Kasn-w/omnitrix-replica/omitrix/activate.h

const unsigned char activate[] = {
0x52, 0x49, 0x46, 0x46, 0xBE, 0xAD, 0x00, 0x00, 0x57, 0x41, 0x56, 0x45, 0x66, 0x6D, 0x74, 0x20, 
0x10, 0x00, 0x00, 0x00, 0x01, 0x00, 0x02, 0x00, 0x80, 0x3E, 0x00, 0x00, 0x00, 0xFA, 0x00, 0x00, 
0x04, 0x00, 0x10, 0x00, 0x64, 0x61, 0x74, 0x61, 0xE4, 0xAC, 0x00, 0x00, 0x00, 0x00, 0xFD, 0xFF, 
0x00, 0x00, 0x03, 0x00, 0x00, 0x00, 0xE5, 0xF9, 0x00, 0x00, 0x03, 0x00, 0xE9, 0xF9, 0xE6, 0xF9, 
0xFE, 0xFF, 0xFF, 0xFF, 0x03, 0x00, 0xE6, 0xF9, 0xE2, 0xF9, 0x05, 0x00, 0x06, 0x00, 0xE0, 0xF9, 
0xE3, 0xF9, 0x09, 0x00, 0x07, 0x00, 0xFA, 0xFF, 0xF4, 0xFF, 0xEC, 0xF9, 0xF4, 0xF9, 0xFB, 0xFF, 
0xF7, 0xFF, 0x08, 0x00, 0xEF, 0xF9, 0xDE, 0xF9, 0xFB, 0xFF, 0x07, 0x00, 0xE8, 0xF9, 0xE8, 0xF9, 
0x00, 0x00, 0xFA, 0xFF, 0x06, 0x00, 0xEE, 0xF9, 0xF7, 0xFF, 0xFD, 0xFF, 0x0C, 0x00, 0x00, 0x00, 
0xF5, 0xFF, 0xEC, 0xF9, 0x04, 0x00, 0xFC, 0xFF, 0xEA, 0xF9, 0xE6, 0xF9, 0xFB, 0xFF, 0x06, 0x00, 
0xF1, 0xF9, 0xE1, 0xF9, 0xFB, 0xFF, 0x09, 0x00, 0xE7, 0xF9, 0xDE, 0xF9, 0xE6, 0xF9, 0x0A, 0x00, 
0x05, 0x00, 0xDF, 0xF9, 0xE1, 0xF9, 0x06, 0x00, 0xF2, 0xF9, 0xFE, 0xFF, 0xF6, 0xFF, 0xE3, 0xF9, 
0xED, 0xF9, 0x0C, 0x00, 0x01, 0x00, 0xDC, 0xF9, 0xE5, 0xF9, 0x06, 0x00, 0xFF, 0xFF, 0xE9, 0xF9, 
0xED, 0xF9, 0xF9, 0xFF, 0xFB, 0xFF, 0xEF, 0xF9, 0xEB, 0xF9, 0xFC, 0xFF, 0x00, 0x00, 0xEA, 0xF9, 
0xE5, 0xF9, 0x01, 0x00, 0x04, 0x00, 0xE4, 0xF9, 0xFB, 0xFF, 0x05, 0x00, 0xEE, 0xF9, 0xFA, 0xFF, 
0xFA, 0xFF, 0xEF, 0xF9, 0xEE, 0xF9, 0xFD, 0xFF, 0xFA, 0xFF, 0xE4, 0xF9, 0x03, 0x00, 0xED, 0xF9, 
0xE8, 0xF9, 0xFC, 0xFF, 0x01, 0x00, 0xEB, 0xF9, 0xE7, 0xF9, 0x01, 0x00, 0xFE, 0xFF, 0xE4, 0xF9, 
0x02, 0x00, 0x01, 0x00, 0x01, 0x00, 0xE5, 0xF9, 0xE5, 0xF9, 0x06, 0x00, 0x06, 0x00, 0xE2, 0xF9, 
0xDC, 0xF9, 0x09, 0x00, 0x10, 0x00, 0xF1, 0xFF, 0xEF, 0xFF, 0xFB, 0xF9, 0xF7, 0xF9, 0xEA, 0xFF, 
0xF4, 0xFF, 0xFE, 0xF9, 0xF1, 0xF9, 0xEE, 0xFF, 0xFB, 0xFF, 0x0B, 0x00, 0xE6, 0xF9, 0xFC, 0xFF, 
0x06, 0x00, 0xE9, 0xF9, 0xFA, 0xFF, 0xFF, 0xFF, 0xEB, 0xF9, 0xEA, 0xF9, 0x04, 0x00, 0xFA, 0xFF, 
0xDD, 0xF9, 0xEF, 0xF9, 0x0C, 0x00, 0xF9, 0xFF, 0xF7, 0xFF, 0x0B, 0x00, 0xEB, 0xF9, 0xDD, 0xF9, 
0x04, 0x00, 0x08, 0x00, 0xFB, 0xFF, 0xF8, 0xFF, 0xEB, 0xF9, 0xED, 0xF9, 0xFD, 0xFF, 0x02, 0x00, 
0xEB, 0xF9, 0xE3, 0xF9, 0xFE, 0xFF, 0x06, 0x00, 0xE9, 0xF9, 0xF9, 0xFF, 0x00, 0x00, 0xED, 0xF9, 
0xE9, 0xF9, 0xFE, 0xFF, 0xFB, 0xFF, 0xE7, 0xF9, 0xEF, 0xF9, 0x05, 0x00, 0xF8, 0xFF, 0xF7, 0xFF, 
0x08, 0x00, 0xF2, 0xF9, 0xE1, 0xF9, 0xF6, 0xFF, 0x04, 0x00, 0xEF, 0xF9, 0xE8, 0xF9, 0x00, 0x00, 
0xFD, 0xFF, 0xFC, 0xFF, 0xEB, 0xF9, 0x05, 0x00, 0xFA, 0xFF, 0xF7, 0xFF, 0xF2, 0xF9, 0x09, 0x00, 
0xF3, 0xFF, 0xFA, 0xFF, 0xF5, 0xF9, 0xEE, 0xF9, 0xF3, 0xFF, 0xFC, 0xFF, 0xF5, 0xF9, 0xEB, 0xF9, 
0xF4, 0xFF, 0xFB, 0xFF, 0xF1, 0xF9, 0x04, 0x00, 0xF7, 0xFF, 0xE4, 0xF9, 0xEE, 0xF9, 0x06, 0x00, 
0x00, 0x00, 0xE4, 0xF9, 0xFD, 0xFF, 0x03, 0x00, 0x04, 0x00, 0xE4, 0xF9, 0xFE, 0xFF, 0x04, 0x00, 
0xFC, 0xFF, 0xFD, 0xFF, 0x08, 0x00, 0xEA, 0xF9, 0xFA, 0xFF, 0x00, 0x00, 0x03, 0x00, 0xE4, 0xF9, 
0xFD, 0xFF, 0x08, 0x00, 0xEB, 0xF9, 0xE0, 0xF9, 0xFE, 0xFF, 0x05, 0x00, 0xEA, 0xF9, 0xE7, 0xF9, 
0xFE, 0xFF, 0xFD, 0xFF, 0xE8, 0xF9, 0xED, 0xF9, 0x00, 0x00, 0xFA, 0xFF, 0xEB, 0xF9, 0xEC, 0xF9, 
0xFD, 0xFF, 0x02, 0x00, 0xE9, 0xF9, 0xE0, 0xF9, 0xE8, 0xF9, 0x0C, 0x00, 0x00, 0x00, 0xF0, 0xFF, 
0xE8, 0xF9, 0xFA, 0xF9, 0x00, 0x00, 0xF0, 0xFF, 0xE9, 0xF9, 0xF3, 0xF9, 0xFC, 0xFF, 0xFB, 0xFF, 
0xEC, 0xF9, 0xE7, 0xF9, 0x00, 0x00, 0x05, 0x00, 0xE5, 0xF9, 0xFB, 0xFF, 0x03, 0x00, 0xEA, 0xF9, 
0xE6, 0xF9, 0x02, 0x00, 0x01, 0x00, 0xE3, 0xF9, 0x00, 0x00, 0x08, 0x00, 0xEC, 0xF9, 0xDB, 0xF9, 
0xF5, 0xFF, 0x13, 0x00, 0xF4, 0xF9, 0xEA, 0xFF, 0xF7, 0xFF, 0x13, 0x00, 0xF1, 0xF9, 0xF0, 0xFF, 
0xF5, 0xFF, 0x10, 0x00, 0xF0, 0xF9, 0xDC, 0xF9, 0xFB, 0xFF, 0xF1, 0xF9, 0xEB, 0xF9, 0xF8, 0xFF, 
0xFF, 0xFF, 0xE9, 0xF9, 0xE7, 0xF9, 0x05, 0x00, 0xFE, 0xFF, 0xFC, 0xFF, 0xED, 0xF9, 0xEC, 0xF9, 
0xFF, 0xFF, 0xFA, 0xFF, 0xFE, 0xFF, 0xED, 0xF9, 0xEA, 0xF9, 0xFB, 0xFF, 0xFB, 0xFF, 0x06, 0x00, 
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
};
