Kasn-w/omnitrix-replica/omitrix/openup.h

const unsigned char openup[] = {
0x52, 0x49, 0x46, 0x46, 0x2E, 0x76, 0x00, 0x00, 0x57, 0x41, 0x56, 0x45, 0x66, 0x6D, 0x74, 0x20, 
0x10, 0x00, 0x00, 0x00, 0x01, 0x00, 0x02, 0x00, 0x80, 0x3E, 0x00, 0x00, 0x00, 0xFA, 0x00, 0x00, 
0x04, 0x00, 0x10, 0x00, 0x64, 0x61, 0x74, 0x61, 0x54, 0x75, 0x00, 0x00, 0x00, 0x00, 0x00, 0x00, 
0x00, 0x00, 0x00, 0x00, 0x00, 0x00, 0x01, 0x00, 0x39, 0xFE, 0xFE, 0xFF, 0x00, 0x00, 0x03, 0x00, 
0x38, 0xFE, 0xFC, 0xFF, 0x01, 0x00, 0x3D, 0xFE, 0x37, 0xFE, 0xFD, 0xFF, 0x02, 0x00, 0x3A, 0xFE, 
0x37, 0xFE, 0x00, 0x00, 0x02, 0x00, 0x39, 0xFE, 0x36, 0xFE, 0xFF, 0xFF, 0x02, 0x00, 0x3B, 0xFE, 
0xFF, 0xFF, 0xFD, 0xFF, 0x39, 0xFE, 0x03, 0x00, 0x00, 0x00, 0x36, 0xFE, 0x39, 0xFE, 0x03, 0x00, 
0xFF, 0xFF, 0x36, 0xFE, 0x3B, 0xFE, 0x02, 0x00, 0xFD, 0xFF, 0x38, 0xFE, 0x3C, 0xFE, 0xFF, 0xFF, 
0xFE, 0xFF, 0x03, 0x00, 0x39, 0xFE, 0x35, 0xFE, 0x01, 0x00, 0x03, 0x00, 0x37, 0xFE, 0xFD, 0xFF, 
0x03, 0x00, 0x3C, 0xFE, 0x37, 0xFE, 0xFE, 0xFF, 0x00, 0x00, 0x3A, 0xFE, 0x39, 0xFE, 0x00, 0x00, 
0xFF, 0xFF, 0x36, 0xFE, 0x3A, 0xFE, 0x04, 0x00, 0x00, 0x00, 0x35, 0xFE, 0x38, 0xFE, 0x04, 0x00, 
0x00, 0x00, 0x35, 0xFE, 0x01, 0x00, 0x03, 0x00, 0x37, 0xFE, 0x36, 0xFE, 0x01, 0x00, 0x3B, 0xFE, 
0x39, 0xFE, 0xFF, 0xFF, 0xFF, 0xFF, 0x38, 0xFE, 0x3A, 0xFE, 0x02, 0x00, 0xFF, 0xFF, 0x37, 0xFE, 
0x39, 0xFE, 0x02, 0x00, 0x00, 0x00, 0xFE, 0xFF, 0x00, 0x00, 0x01, 0x00, 0x39, 0xFE, 0x38, 0xFE, 
0x00, 0x00, 0x01, 0x00, 0x00, 0x00, 0x39, 0xFE, 0x38, 0xFE, 0xFE, 0xFF, 0x01, 0x00, 0x3B, 0xFE, 
0x38, 0xFE, 0xFE, 0xFF, 0x3A, 0xFE, 0x01, 0x00, 0xFF, 0xFF, 0x01, 0x00, 0x39, 0xFE, 0xFD, 0xFF, 
0xFF, 0xFF, 0x04, 0x00, 0x03, 0x00, 0x34, 0xFE, 0x35, 0xFE, 0x3E, 0xFE, 0x04, 0x00, 0xFB, 0xFF, 
0xFB, 0xFF, 0x3D, 0xFE, 0x3E, 0xFE, 0xFD, 0xFF, 0xFB, 0xFF, 0x3A, 0xFE, 0x3E, 0xFE, 0x00, 0x00, 
0xFB, 0xFF, 0x38, 0xFE, 0x04, 0x00, 0x00, 0x00, 0xFD, 0xFF, 0x3A, 0xFE, 0x3A, 0xFE, 0xFE, 0xFF, 
0x00, 0x00, 0x3C, 0xFE, 0x39, 0xFE, 0xFC, 0xFF, 0xFF, 0xFF, 0x3C, 0xFE, 0x3B, 0xFE, 0xFD, 0xFF, 
0x35, 0xFE, 0x3C, 0xFE, 0x04, 0x00, 0xFD, 0xFF, 0x36, 0xFE, 0x3C, 0xFE, 0x01, 0x00, 0xFD, 0xFF, 
0x3A, 0xFE, 0x02, 0x00, 0xFE, 0xFF, 0x38, 0xFE, 0x3A, 0xFE, 0x00, 0x00, 0x00, 0x00, 0x39, 0xFE, 
0x38, 0xFE, 0x00, 0x00, 0x01, 0x00, 0x00, 0x00, 0x38, 0xFE, 0x39, 0xFE, 0x00, 0x00, 0x00, 0x00, 
0x01, 0x00, 0x39, 0xFE, 0xFF, 0xFF, 0xFF, 0xFF, 0x39, 0xFE, 0x3A, 0xFE, 0x00, 0x00, 0xFF, 0xFF, 
0x39, 0xFE, 0x39, 0xFE, 0xFF, 0xFF, 0x01, 0x00, 0x02, 0x00, 0xFD, 0xFF, 0xFE, 0xFF, 0x04, 0x00, 
0x3A, 0xFE, 0x35, 0xFE, 0xFF, 0xFF, 0x03, 0x00, 0x39, 0xFE, 0x37, 0xFE, 0x01, 0x00, 0x01, 0x00, 
0xFE, 0xFF, 0x37, 0xFE, 0x3B, 0xFE, 0x03, 0x00, 0xFD, 0xFF, 0x35, 0xFE, 0x3C, 0xFE, 0x04, 0x00, 
0xFD, 0xFF, 0xFD, 0xFF, 0x02, 0x00, 0x3B, 0xFE, 0x38, 0xFE, 0xFF, 0xFF, 0xFF, 0xFF, 0xFF, 0xFF, 
0x3B, 0xFE, 0x01, 0x00, 0xFD, 0xFF, 0x39, 0xFE, 0x3C, 0xFE, 0xFF, 0xFF, 0xFE, 0xFF, 0x3C, 0xFE, 
0x00, 0x00, 0xFB, 0xFF, 0x3A, 0xFE, 0x04, 0x00, 0xFF, 0xFF, 0x37, 0xFE, 0x39, 0xFE, 0x00, 0x00, 
0x00, 0x00, 0x3A, 0xFE, 0x39, 0xFE, 0xFF, 0xFF, 0x00, 0x00, 0x39, 0xFE, 0x00, 0x00, 0x01, 0x00, 
0x38, 0xFE, 0x37, 0xFE, 0x01, 0x00, 0x02, 0x00, 0x38, 0xFE, 0x37, 0xFE, 0x01, 0x00, 0x02, 0x00, 
0x38, 0xFE, 0x36, 0xFE, 0x00, 0x00, 0x04, 0x00, 0x00, 0x00, 0xFC, 0xFF, 0x39, 0xFE, 0x04, 0x00, 
0x00, 0x00, 0xFC, 0xFF, 0x38, 0xFE, 0x3B, 0xFE, 0x02, 0x00, 0x00, 0x00, 0x36, 0xFE, 0x39, 0xFE, 
0x02, 0x00, 0xFF, 0xFF, 0x00, 0x00, 0x3A, 0xFE, 0xFE, 0xFF, 0xFE, 0xFF, 0x3C, 0xFE, 0x3C, 0xFE, 
0xFD, 0xFF, 0xFD, 0xFF, 0x3B, 0xFE, 0x02, 0x00, 0xFE, 0xFF, 0xFF, 0xFF, 0x3B, 0xFE, 0x00, 0x00, 
0xFE, 0xFF, 0x3A, 0xFE, 0x01, 0x00, 0xFE, 0xFF, 0x00, 0x00, 0x3B, 0xFE, 0x39, 0xFE, 0xFE, 0xFF, 
0xFF, 0xFF, 0x3B, 0xFE, 0x39, 0xFE, 0xFD, 0xFF, 0x01, 0x00, 0x03, 0x00, 0x37, 0xFE, 0xFE, 0xFF, 
0x02, 0x00, 0x01, 0x00, 0x37, 0xFE, 0x00, 0x00, 0x00, 0x00, 0xFF, 0xFF, 0x3B, 0xFE, 0x01, 0x00, 
0xFE, 0xFF, 0x38, 0xFE, 0x01, 0x00, 0x01, 0x00, 0x38, 0xFE, 0x37, 0xFE, 0xFF, 0xFF, 0x02, 0x00, 
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
};
