Kasn-w/omnitrix-replica/omitrix/selecte.h

const unsigned char selecte[] = {
0x52, 0x49, 0x46, 0x46, 0xEA, 0x52, 0x00, 0x00, 0x57, 0x41, 0x56, 0x45, 0x66, 0x6D, 0x74, 0x20, 
0x10, 0x00, 0x00, 0x00, 0x01, 0x00, 0x02, 0x00, 0x80, 0x3E, 0x00, 0x00, 0x00, 0xFA, 0x00, 0x00, 
0x04, 0x00, 0x10, 0x00, 0x64, 0x61, 0x74, 0x61, 0x10, 0x52, 0x00, 0x00, 0x0E, 0xF8, 0x0F, 0xF8, 
0x10, 0xF8, 0x0D, 0xF8, 0x0D, 0xF8, 0x10, 0xF8, 0x10, 0xF8, 0xFF, 0xFF, 0x0D, 0xF8, 0x10, 0xF8, 
0x0F, 0xF8, 0xFE, 0xFF, 0x0F, 0xF8, 0x10, 0xF8, 0x0D, 0xF8, 0xFF, 0xFF, 0x11, 0xF8, 0x0E, 0xF8, 
0x0B, 0xF8, 0x02, 0x00, 0x13, 0xF8, 0x0D, 0xF8, 0x09, 0xF8, 0x0E, 0xF8, 0x13, 0xF8, 0x11, 0xF8, 
0x0C, 0xF8, 0x0B, 0xF8, 0x10, 0xF8, 0x12, 0xF8, 0x0E, 0xF8, 0x0B, 0xF8, 0xFF, 0xFF, 0x12, 0xF8, 
0x10, 0xF8, 0xFD, 0xFF, 0x0E, 0xF8, 0x11, 0xF8, 0x0F, 0xF8, 0x0D, 0xF8, 0x0F, 0xF8, 0x0F, 0xF8, 
0xFF, 0xFF, 0x00, 0x00, 0x0E, 0xF8, 0x01, 0x00, 0x02, 0x00, 0xFE, 0xFF, 0x0C, 0xF8, 0x02, 0x00, 
0x04, 0x00, 0xFE, 0xFF, 0x0B, 0xF8, 0x02, 0x00, 0x10, 0xF8, 0x0D, 0xF8, 0x0D, 0xF8, 0x01, 0x00, 
0x02, 0x00, 0x0E, 0xF8, 0x0D, 0xF8, 0xFF, 0xFF, 0x10, 0xF8, 0x11, 0xF8, 0x0D, 0xF8, 0xFD, 0xFF, 
0x00, 0x00, 0x12, 0xF8, 0x02, 0x00, 0xFC, 0xFF, 0xFE, 0xFF, 0x12, 0xF8, 0x0F, 0xF8, 0xFD, 0xFF, 
0x01, 0x00, 0x12, 0xF8, 0xFE, 0xFF, 0xFD, 0xFF, 0x02, 0x00, 0x02, 0x00, 0xFF, 0xFF, 0xFE, 0xFF, 
0x00, 0x00, 0x02, 0x00, 0x01, 0x00, 0xFE, 0xFF, 0xFE, 0xFF, 0x12, 0xF8, 0x11, 0xF8, 0xFC, 0xFF, 
0xFE, 0xFF, 0x11, 0xF8, 0x01, 0x00, 0xFF, 0xFF, 0x0E, 0xF8, 0x0E, 0xF8, 0x00, 0x00, 0x11, 0xF8, 
0x0F, 0xF8, 0x0C, 0xF8, 0x00, 0x00, 0x01, 0x00, 0x0E, 0xF8, 0x0F, 0xF8, 0x0F, 0xF8, 0xFE, 0xFF, 
0x0D, 0xF8, 0x12, 0xF8, 0x03, 0x00, 0xFB, 0xFF, 0xFD, 0xFF, 0x06, 0x00, 0x11, 0xF8, 0x08, 0xF8, 
0xFD, 0xFF, 0x07, 0x00, 0x12, 0xF8, 0x08, 0xF8, 0x0B, 0xF8, 0x13, 0xF8, 0x12, 0xF8, 0x0C, 0xF8, 
0x0C, 0xF8, 0x10, 0xF8, 0x01, 0x00, 0xFF, 0xFF, 0x00, 0x00, 0x10, 0xF8, 0x0E, 0xF8, 0x0C, 0xF8, 
0x00, 0x00, 0x03, 0x00, 0x01, 0x00, 0xFE, 0xFF, 0x0D, 0xF8, 0x0F, 0xF8, 0x11, 0xF8, 0x0F, 0xF8, 
0x0B, 0xF8, 0x0D, 0xF8, 0x12, 0xF8, 0x02, 0x00, 0x0C, 0xF8, 0x0D, 0xF8, 0x10, 0xF8, 0x10, 0xF8, 
0x00, 0x00, 0xFE, 0xFF, 0x0E, 0xF8, 0x10, 0xF8, 0x0F, 0xF8, 0xFF, 0xFF, 0x00, 0x00, 0x0F, 0xF8, 
0x0E, 0xF8, 0x0F, 0xF8, 0x01, 0x00, 0xFF, 0xFF, 0x0D, 0xF8, 0x0F, 0xF8, 0x10, 0xF8, 0x00, 0x00, 
0x0E, 0xF8, 0x0E, 0xF8, 0x0E, 0xF8, 0x00, 0x00, 0x10, 0xF8, 0x0F, 0xF8, 0x0C, 0xF8, 0x00, 0x00, 
0x03, 0x00, 0x0F, 0xF8, 0xFD, 0xFF, 0xFE, 0xFF, 0x11, 0xF8, 0x12, 0xF8, 0xFF, 0xFF, 0xFC, 0xFF, 
0x00, 0x00, 0x12, 0xF8, 0x0E, 0xF8, 0xFE, 0xFF, 0x00, 0x00, 0x10, 0xF8, 0x10, 0xF8, 0xFF, 0xFF, 
0xFD, 0xFF, 0x10, 0xF8, 0x04, 0x00, 0xFD, 0xFF, 0xFB, 0xFF, 0x12, 0xF8, 0x05, 0x00, 0xFE, 0xFF, 
0xFC, 0xFF, 0x01, 0x00, 0x02, 0x00, 0x0E, 0xF8, 0xFF, 0xFF, 0x00, 0x00, 0x00, 0x00, 0x0E, 0xF8, 
0x02, 0x00, 0x01, 0x00, 0xFD, 0xFF, 0x00, 0x00, 0x03, 0x00, 0x00, 0x00, 0xFE, 0xFF, 0xFF, 0xFF, 
0x00, 0x00, 0x0F, 0xF8, 0x10, 0xF8, 0x01, 0x00, 0xFF, 0xFF, 0x0D, 0xF8, 0x00, 0x00, 0x01, 0x00, 
0x01, 0x00, 0x00, 0x00, 0xFE, 0xFF, 0xFF, 0xFF, 0x11, 0xF8, 0x02, 0x00, 0xFE, 0xFF, 0xFE, 0xFF, 
0x0F, 0xF8, 0x01, 0x00, 0x01, 0x00, 0x00, 0x00, 0xFE, 0xFF, 0x00, 0x00, 0x03, 0x00, 0x00, 0x00, 
0x0C, 0xF8, 0x00, 0x00, 0x01, 0x00, 0x00, 0x00, 0x0E, 0xF8, 0x00, 0x00, 0x01, 0x00, 0x00, 0x00, 
0xFF, 0xFF, 0x01, 0x00, 0x0F, 0xF8, 0xFE, 0xFF, 0x01, 0x00, 0x02, 0x00, 0xFD, 0xFF, 0x0D, 0xF8, 
0x04, 0x00, 0x00, 0x00, 0xFD, 0xFF, 0x02, 0x00, 0x01, 0x00, 0xFD, 0xFF, 0x00, 0x00, 0x03, 0x00, 
0x00, 0x00, 0xFE, 0xFF, 0x0F, 0xF8, 0x0F, 0xF8, 0xFF, 0xFF, 0x01, 0x00, 0x10, 0xF8, 0x0D, 0xF8, 
0xFE, 0xFF, 0x00, 0x00, 0x02, 0x00, 0x11, 0xF8, 0x0D, 0xF8, 0xFD, 0xFF, 0x02, 0x00, 0x11, 0xF8, 
0x0B, 0xF8, 0xFE, 0xFF, 0x04, 0x00, 0x0F, 0xF8, 0x0C, 0xF8, 0x01, 0x00, 0x01, 0x00, 0xFF, 0xFF, 
0x00, 0x00, 0x00, 0x00, 0xFF, 0xFF, 0x00, 0x00, 0x00, 0x00, 0x01, 0x00, 0x02, 0x00, 0xFE, 0xFF, 
0xFE, 0xFF, 0x03, 0x00, 0x02, 0x00, 0xFC, 0xFF, 0xFE, 0xFF, 0x04, 0x00, 0x00, 0x00, 0x0B, 0xF8, 
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
};
