Kasn-w/omnitrix-replica/omitrix/wait.h

const unsigned char wait[] = {
0x52, 0x49, 0x46, 0x46, 0xBE, 0x2E, 0x00, 0x00, 0x57, 0x41, 0x56, 0x45, 0x66, 0x6D, 0x74, 0x20, 
0x10, 0x00, 0x00, 0x00, 0x01, 0x00, 0x02, 0x00, 0x80, 0x3E, 0x00, 0x00, 0x00, 0xFA, 0x00, 0x00, 
0x04, 0x00, 0x10, 0x00, 0x64, 0x61, 0x74, 0x61, 0xE4, 0x2D, 0x00, 0x00, 0x00, 0x00, 0x00, 0x00, 
0x60, 0xFA, 0x61, 0xFA, 0x61, 0xFA, 0x5F, 0xFA, 0x00, 0x00, 0x01, 0x00, 0x00, 0x00, 0x00, 0x00, 
0x60, 0xFA, 0x60, 0xFA, 0x61, 0xFA, 0x61, 0xFA, 0xFE, 0xFF, 0xFF, 0xFF, 0x03, 0x00, 0x00, 0x00, 
0x5D, 0xFA, 0x62, 0xFA, 0x65, 0xFA, 0x5E, 0xFA, 0xFA, 0xFF, 0x04, 0x00, 0x05, 0x00, 0xFB, 0xFF, 
0x5D, 0xFA, 0x64, 0xFA, 0x63, 0xFA, 0x5F, 0xFA, 0xFE, 0xFF, 0x01, 0x00, 0x01, 0x00, 0xFF, 0xFF, 
0x5F, 0xFA, 0x61, 0xFA, 0x63, 0xFA, 0x60, 0xFA, 0xFD, 0xFF, 0x01, 0x00, 0x04, 0x00, 0xFF, 0xFF, 
0x5C, 0xFA, 0x61, 0xFA, 0x63, 0xFA, 0x5F, 0xFA, 0xFF, 0xFF, 0x02, 0x00, 0x00, 0x00, 0x5F, 0xFA, 
0x62, 0xFA, 0x61, 0xFA, 0xFF, 0xFF, 0x60, 0xFA, 0xFF, 0xFF, 0x00, 0x00, 0x01, 0x00, 0x61, 0xFA, 
0x60, 0xFA, 0x5F, 0xFA, 0x00, 0x00, 0x02, 0x00, 0x01, 0x00, 0xFE, 0xFF, 0x5F, 0xFA, 0x62, 0xFA, 
0x61, 0xFA, 0x5F, 0xFA, 0x00, 0x00, 0x02, 0x00, 0x00, 0x00, 0xFD, 0xFF, 0x60, 0xFA, 0x65, 0xFA, 
0x61, 0xFA, 0x5B, 0xFA, 0x00, 0x00, 0x05, 0x00, 0xFF, 0xFF, 0xFC, 0xFF, 0x62, 0xFA, 0x63, 0xFA, 
0x5F, 0xFA, 0x5F, 0xFA, 0x01, 0x00, 0x00, 0x00, 0xFF, 0xFF, 0x02, 0x00, 0x62, 0xFA, 0x5D, 0xFA, 
0x5F, 0xFA, 0x64, 0xFA, 0x01, 0x00, 0xFC, 0xFF, 0xFF, 0xFF, 0x03, 0x00, 0x61, 0xFA, 0x5F, 0xFA, 
0x61, 0xFA, 0x61, 0xFA, 0xFF, 0xFF, 0x00, 0x00, 0x01, 0x00, 0xFF, 0xFF, 0x5F, 0xFA, 0x63, 0xFA, 
0x61, 0xFA, 0x5D, 0xFA, 0x02, 0x00, 0x03, 0x00, 0x5D, 0xFA, 0x5E, 0xFA, 0x64, 0xFA, 0x62, 0xFA, 
0xFC, 0xFF, 0x00, 0x00, 0x04, 0x00, 0x00, 0x00, 0x5D, 0xFA, 0x60, 0xFA, 0x64, 0xFA, 0x60, 0xFA, 
0xFC, 0xFF, 0x01, 0x00, 0x04, 0x00, 0xFF, 0xFF, 0x5D, 0xFA, 0x62, 0xFA, 0x62, 0xFA, 0x5F, 0xFA, 
0x00, 0x00, 0x01, 0x00, 0xFF, 0xFF, 0xFF, 0xFF, 0x62, 0xFA, 0x62, 0xFA, 0x60, 0xFA, 0x5F, 0xFA, 
0xFE, 0xFF, 0x01, 0x00, 0x03, 0x00, 0xFF, 0xFF, 0x5E, 0xFA, 0x61, 0xFA, 0x62, 0xFA, 0x61, 0xFA, 
0x00, 0x00, 0xFF, 0xFF, 0xFF, 0xFF, 0x01, 0x00, 0x61, 0xFA, 0x5F, 0xFA, 0x00, 0x00, 0x01, 0x00, 
0x00, 0x00, 0x00, 0x00, 0x60, 0xFA, 0x60, 0xFA, 0x61, 0xFA, 0x62, 0xFA, 0xFF, 0xFF, 0xFE, 0xFF, 
0x02, 0x00, 0x01, 0x00, 0xFD, 0xFF, 0x00, 0x00, 0x63, 0xFA, 0x60, 0xFA, 0xFE, 0xFF, 0x01, 0x00, 
0x02, 0x00, 0xFF, 0xFF, 0x5F, 0xFA, 0x61, 0xFA, 0x61, 0xFA, 0x60, 0xFA, 0x00, 0x00, 0x01, 0x00, 
0x00, 0x00, 0xFE, 0xFF, 0x60, 0xFA, 0x63, 0xFA, 0x60, 0xFA, 0x5E, 0xFA, 0x02, 0x00, 0x02, 0x00, 
0xFD, 0xFF, 0xFF, 0xFF, 0x64, 0xFA, 0x60, 0xFA, 0xFC, 0xFF, 0x02, 0x00, 0x03, 0x00, 0xFD, 0xFF, 
0xFE, 0xFF, 0x03, 0x00, 0x62, 0xFA, 0x5E, 0xFA, 0xFF, 0xFF, 0x62, 0xFA, 0x00, 0x00, 0x00, 0x00, 
0x01, 0x00, 0xFE, 0xFF, 0x5F, 0xFA, 0x62, 0xFA, 0x62, 0xFA, 0x60, 0xFA, 0xFF, 0xFF, 0x00, 0x00, 
0x60, 0xFA, 0x61, 0xFA, 0x62, 0xFA, 0x60, 0xFA, 0xFF, 0xFF, 0x00, 0x00, 0x00, 0x00, 0xFF, 0xFF, 
0x61, 0xFA, 0x62, 0xFA, 0x5F, 0xFA, 0x5F, 0xFA, 0x02, 0x00, 0x01, 0x00, 0xFE, 0xFF, 0x01, 0x00, 
0x62, 0xFA, 0x5E, 0xFA, 0x5F, 0xFA, 0x62, 0xFA, 0x01, 0x00, 0xFF, 0xFF, 0x00, 0x00, 0x01, 0x00, 
0x60, 0xFA, 0x5F, 0xFA, 0x61, 0xFA, 0x63, 0xFA, 0xFF, 0xFF, 0xFD, 0xFF, 0x01, 0x00, 0x02, 0x00, 
0x60, 0xFA, 0x60, 0xFA, 0x00, 0x00, 0xFE, 0xFF, 0x01, 0x00, 0x04, 0x00, 0xFE, 0xFF, 0xFC, 0xFF, 
0x62, 0xFA, 0x64, 0xFA, 0x00, 0x00, 0xFD, 0xFF, 0xFF, 0xFF, 0x02, 0x00, 0x01, 0x00, 0xFE, 0xFF, 
0x60, 0xFA, 0x63, 0xFA, 0x00, 0x00, 0xFE, 0xFF, 0x00, 0x00, 0x01, 0x00, 0x61, 0xFA, 0x61, 0xFA, 
0x5F, 0xFA, 0x5E, 0xFA, 0x01, 0x00, 0x03, 0x00, 0x00, 0x00, 0xFD, 0xFF, 0x61, 0xFA, 0x63, 0xFA, 
0x5E, 0xFA, 0x5F, 0xFA, 0x03, 0x00, 0x61, 0xFA, 0xFD, 0xFF, 0x00, 0x00, 0x63, 0xFA, 0x5F, 0xFA, 
0x5F, 0xFA, 0x62, 0xFA, 0x00, 0x00, 0xFF, 0xFF, 0x00, 0x00, 0x01, 0x00, 0x61, 0xFA, 0x60, 0xFA, 
0x61, 0xFA, 0x60, 0xFA, 0xFF, 0xFF, 0x00, 0x00, 0x61, 0xFA, 0x60, 0xFA, 0x5F, 0xFA, 0x62, 0xFA, 
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
};
